wurthless-elektroniks/clock/src/wurthless/clock/drivers/display/bcdlatchdisplay.py

'''
Display with two SN74HC373s driving four CD4028 chips, or similar configuration
Used with first version of the Nixie driver circuit
'''

import time
from machine import Pin, PWM
from wurthless.clock.api.display import Display,DISPLAY_TYPE_NUMERIC
from wurthless.clock.cvars.cvars import registerCvar

# Latch enable for digits 0/1
registerCvar("wurthless.clock.drivers.display.bcdlatchdisplay",
             "latchenable_dig01_pin",
             "Int",
             13)

# Latch enable for digits 2/3
registerCvar("wurthless.clock.drivers.display.bcdlatchdisplay",
             "latchenable_dig23_pin",
             "Int",
             14)

# Output for digit 0/2 BCD bit 0
registerCvar("wurthless.clock.drivers.display.bcdlatchdisplay",
             "dig02_bit_0_pin",
             "Int",
             15)

# Output for digit 0/2 BCD bit 1
registerCvar("wurthless.clock.drivers.display.bcdlatchdisplay",
             "dig02_bit_1_pin",
             "Int",
             16)

# Output for digit 0/2 BCD bit 2
registerCvar("wurthless.clock.drivers.display.bcdlatchdisplay",
             "dig02_bit_2_pin",
             "Int",
             17)

# Output for digit 0/2 BCD bit 3
registerCvar("wurthless.clock.drivers.display.bcdlatchdisplay",
             "dig02_bit_3_pin",
             "Int",
             18)

# Output for digit 1/3 BCD bit 0
registerCvar("wurthless.clock.drivers.display.bcdlatchdisplay",
             "dig13_bit_0_pin",
             "Int",
             19)

# Output for digit 1/3 BCD bit 1
registerCvar("wurthless.clock.drivers.display.bcdlatchdisplay",
             "dig13_bit_1_pin",
             "Int",
             20)

# Output for digit 1/3 BCD bit 2
registerCvar("wurthless.clock.drivers.display.bcdlatchdisplay",
             "dig13_bit_2_pin",
             "Int",
             21)

# Output for digit 1/3 BCD bit 3
registerCvar("wurthless.clock.drivers.display.bcdlatchdisplay",
             "dig13_bit_3_pin",
             "Int",
             22)

class BcdLatchDisplay(Display):
    def __init__(self, tot):
        cvars = tot.cvars()

        latchenable_dig01_pin = cvars.get("wurthless.clock.drivers.display.bcdlatchdisplay", "latchenable_dig01_pin" )
        latchenable_dig23_pin = cvars.get("wurthless.clock.drivers.display.bcdlatchdisplay", "latchenable_dig23_pin" )

        dig02_bit_0_pin = cvars.get("wurthless.clock.drivers.display.bcdlatchdisplay", "dig02_bit_0_pin" )
        dig02_bit_1_pin = cvars.get("wurthless.clock.drivers.display.bcdlatchdisplay", "dig02_bit_1_pin" )
        dig02_bit_2_pin = cvars.get("wurthless.clock.drivers.display.bcdlatchdisplay", "dig02_bit_2_pin" )
        dig02_bit_3_pin = cvars.get("wurthless.clock.drivers.display.bcdlatchdisplay", "dig02_bit_3_pin" )
        dig13_bit_0_pin = cvars.get("wurthless.clock.drivers.display.bcdlatchdisplay", "dig13_bit_0_pin" )
        dig13_bit_1_pin = cvars.get("wurthless.clock.drivers.display.bcdlatchdisplay", "dig13_bit_1_pin" )
        dig13_bit_2_pin = cvars.get("wurthless.clock.drivers.display.bcdlatchdisplay", "dig13_bit_2_pin" )
        dig13_bit_3_pin = cvars.get("wurthless.clock.drivers.display.bcdlatchdisplay", "dig13_bit_3_pin" )

        self._digit_output_pins = []
        for pin in [ dig02_bit_0_pin, dig02_bit_1_pin, dig02_bit_2_pin, dig02_bit_3_pin, \
                     dig13_bit_0_pin, dig13_bit_1_pin, dig13_bit_2_pin, dig13_bit_3_pin ]:
            pin_obj = Pin(pin, Pin.OUT)
            self._digit_output_pins.append(pin_obj)

        self._latchenable_dig01_pin = Pin(latchenable_dig01_pin, Pin.OUT)
        self._latchenable_dig23_pin = Pin(latchenable_dig23_pin, Pin.OUT)

        self.setDigitsNumeric(None, None, None, None)

    def getDisplayType(self):
        return DISPLAY_TYPE_NUMERIC

    def _latchDigits(self, dig0, dig1):
        output_byte = (dig1 << 4) | dig0
        bitmasks = [ 0x01, 0x02, 0x04, 0x08, 0x10, 0x20, 0x40, 0x80 ]
        for i, bitmask in enumerate(bitmasks):
            self._digit_output_pins[i].value( (output_byte & bitmask) != 0)

    def setDigitsNumeric(self, a, b, c, d):
        digits_out = [ 0xF, 0xF, 0xF, 0xF ]

        if a is not None and 0 <= a <= 9:
            digits_out[0] = a
    
        if b is not None and 0 <= b <= 9:
            digits_out[1] = b
        
        if c is not None and 0 <= c <= 9:
            digits_out[2] = c

        if d is not None and 0 <= d <= 9:
            digits_out[3] = d

        self._latchDigits(digits_out[0], digits_out[1])
        self._latchenable_dig01_pin.value(1)
        time.sleep(0.001)
        self._latchenable_dig01_pin.value(0)
        self._latchDigits(digits_out[2], digits_out[3])
        self._latchenable_dig23_pin.value(1)
        time.sleep(0.001)
        self._latchenable_dig23_pin.value(0)
