wurthless-elektroniks/clock/src/wurthless/clock/drivers/input/resetkeycomboinputs.py

'''
Force hard reset on three-fingered salute (UP/DOWN/SET pressed simultaneously).

Needed for boards that don't have a dedicated reset button.
'''

from wurthless.clock.common.upy import reboot
from wurthless.clock.drivers.input.decoratedinputs import DecoratedInputs

class ResetKeycomboInputs(DecoratedInputs):
    def strobe(self):
        if self.up() and self.down() and self.set():
            reboot()

        return super().strobe()
