wurthless-elektroniks/clock/src/wurthless/clock/common/ntp4timesource.py

from wurthless.clock.cvars.cvars import registerCvar
from wurthless.clock.api.timesource import TimeSource, TIMESOURCE_GENERIC_ERROR
from wurthless.clock.common.ntp4prot import ntpv4_transact

try:
    import usocket as socket
except:
    import socket

# NTP server to use when fetching time.
registerCvar("wurthless.clock.common.ntp4",
             "host",
             "String",
             "pool.ntp.org")

# NTP socket timeout.
registerCvar("wurthless.clock.common.ntp4",
             "timeout",
             "Int",
            1)

class Ntp4TimeSource(TimeSource):
    def __init__(self, tot):
        self.tot = tot

    def getUtcTime(self):
        if self.tot.nic().isUp() is False:
            return TIMESOURCE_GENERIC_ERROR

        try:
            addr = socket.getaddrinfo(self.tot.cvars().get("wurthless.clock.common.ntp4","host"), 123)[0][-1]
            s = socket.socket(socket.AF_INET, socket.SOCK_DGRAM)
            
            def _transact(query):
                s.settimeout(self.tot.cvars().get("wurthless.clock.common.ntp4","timeout"))
                res = s.sendto(query, addr)
                return s.recv(48)
            
            try:
                return ntpv4_transact(lambda q: _transact(q))
            finally:
                s.close()
        except Exception as e:
            print("Ntp4TimeSource: unable to grab time over NTP")
            return TIMESOURCE_GENERIC_ERROR
