wurthless-elektroniks/clock/src/wurthless/clock/drivers/display/invertedbitdisplay.py

#
# Decorator for other display drivers, that inverts all bits being sent in.
#

from wurthless.clock.api.display import Display
from wurthless.clock.drivers.display.sevensegdisplay import SevenSegmentDisplay

class InvertedBitDisplay(SevenSegmentDisplay):
    def __init__(self, parent):
        self.parent = parent

    def setBrightness(self, brightness):
        self.parent.setBrightness(brightness)

    def setDigitsBinary(self, a, b, c, d):
        self.parent.setDigitsBinary(~a, ~b, ~c, ~d)

    def shutdown(self):
        self.parent.shutdown()
