wurthless-elektroniks/clock/src/wurthless/clock/common/bcd.py

def unpackBcd(a: int, b: int) -> list[int]:
    '''
    Unpack two ints into a BCD array.
    '''
    buf = [ 0,0,0,0 ]
    buf[1] = int(a % 10)
    buf[0] = int((a - buf[1]) / 10)
    buf[3] = int(b % 10)
    buf[2] = int((b - buf[3]) / 10)
    return buf
